Aka-O/Medication-Dispensing-System/Misc. Data/Body.png

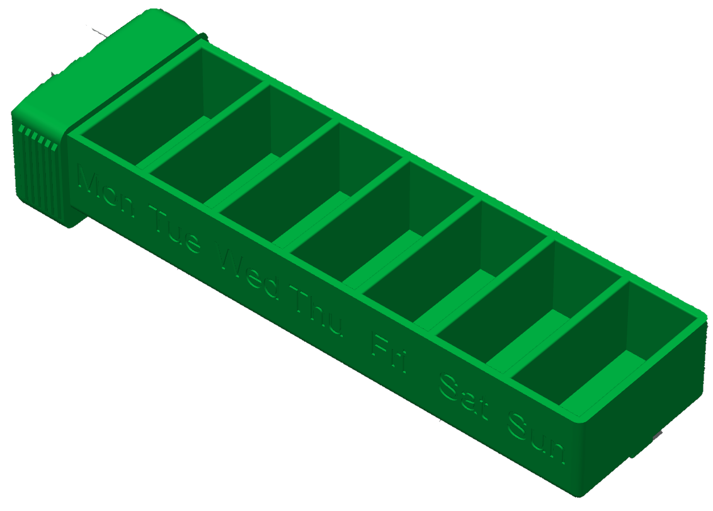
Misc. Data/Body.png
